DSM-Interrupt/FLP/FLP_PCB/FLP_PCB_terminal/mistance_PCB_terminal.kicad_sch

## KiCad design FLP_PCB/FLP_PCB_terminal/mistance_PCB_terminal.kicad_sch (2025-05-16)

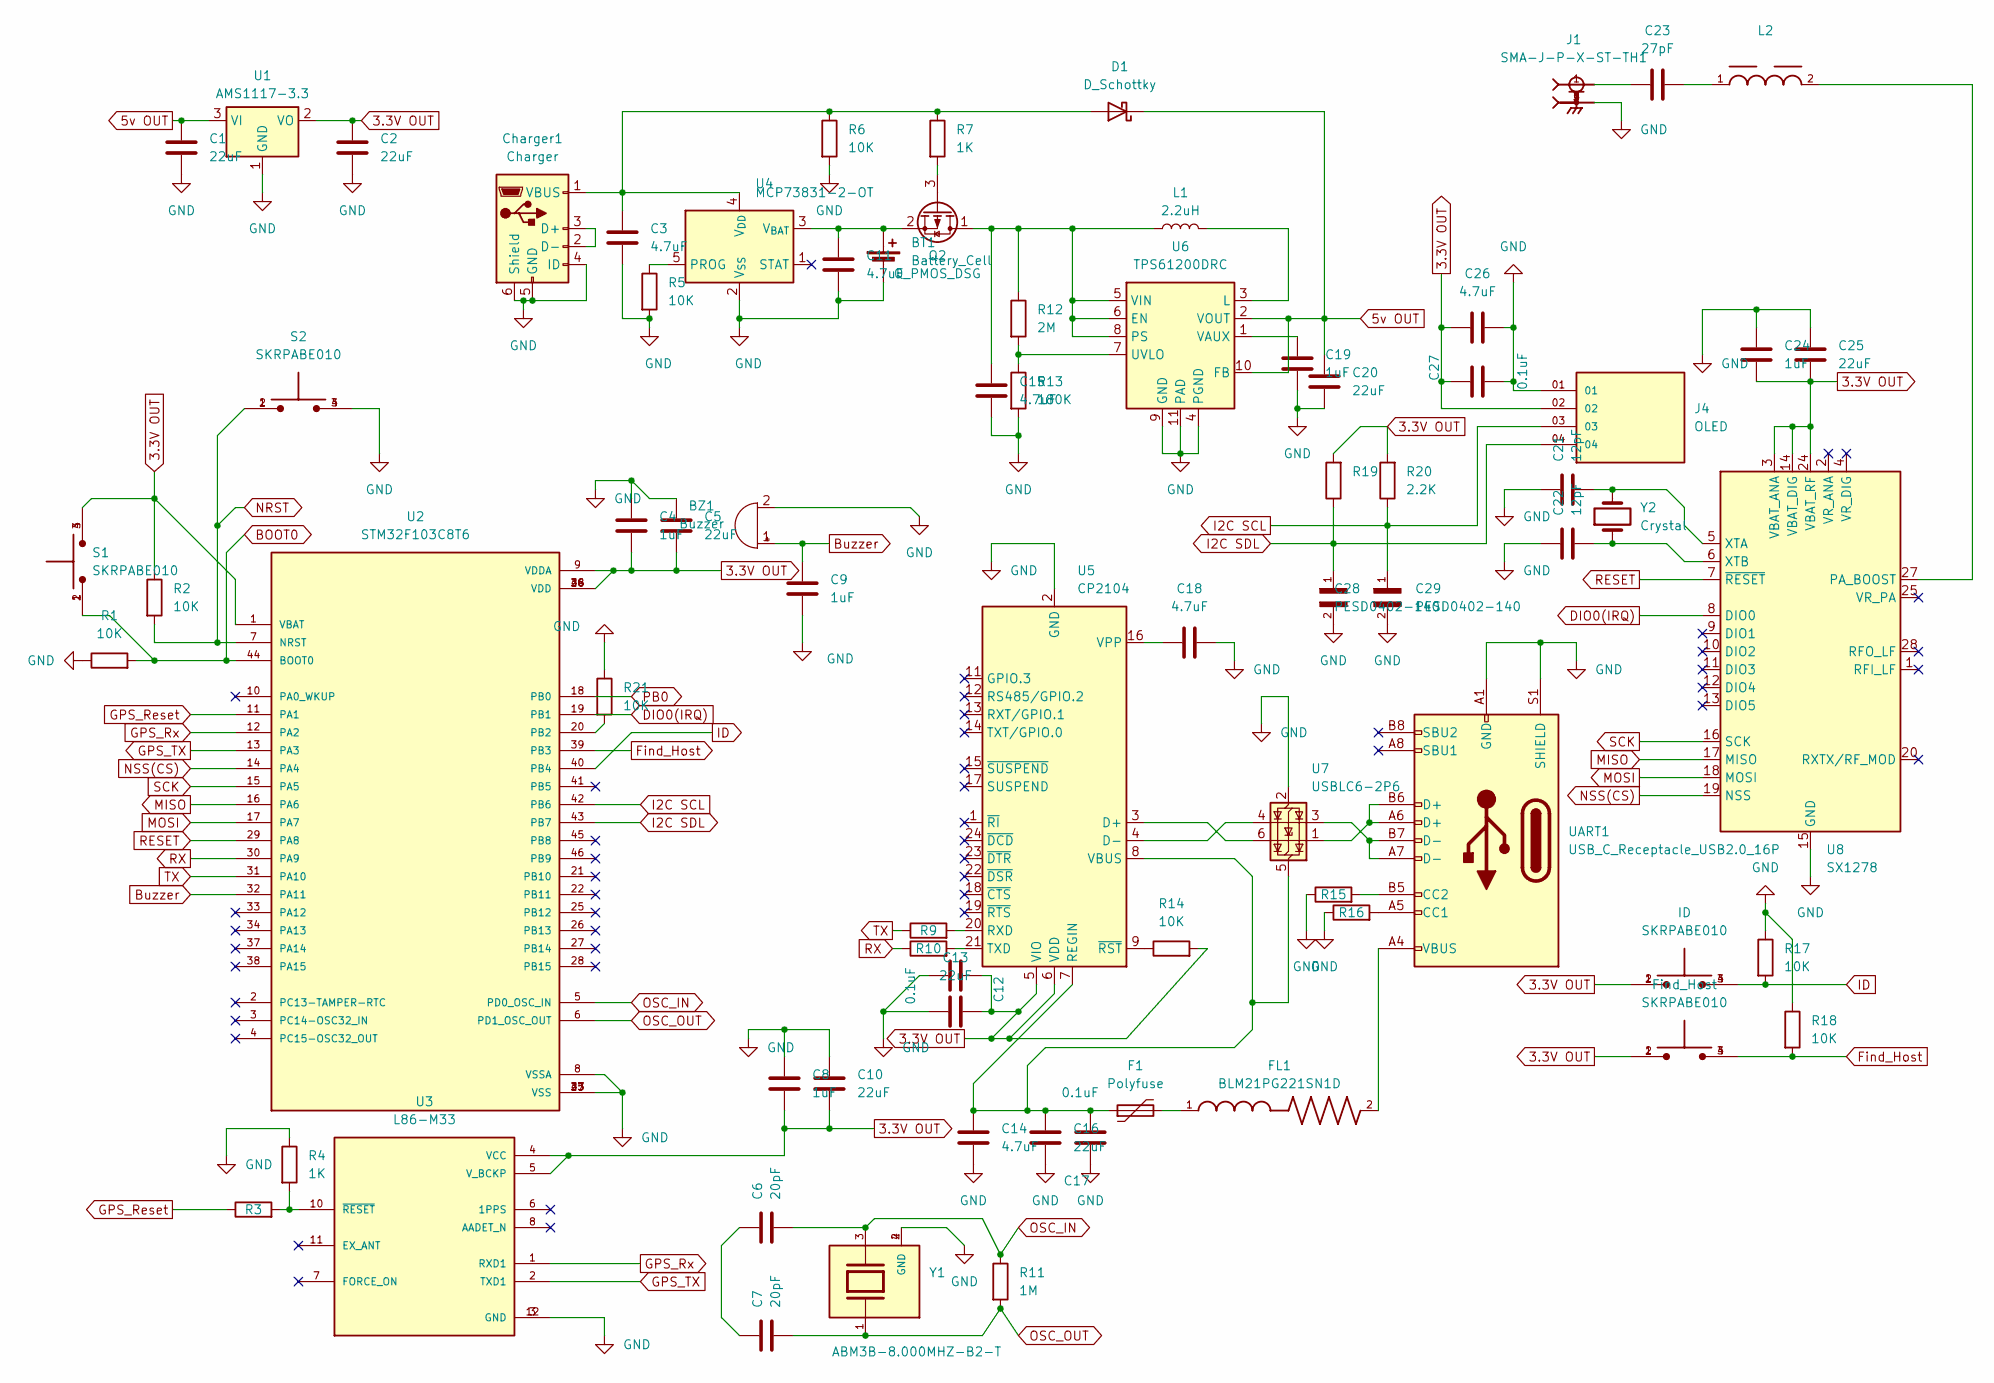
[picture p17: schematic mistance_PCB_terminal.kicad_sch]

Parts:
BT1: Battery_Cell; BatteryHolder_MPD_BH-18650-PC2
BZ1: Buzzer; Buzzer_15x7.5RM7.6
C1, C2, C5, C10, C13, C16, C20, C25: 22uF; C_0805_2012Metric
C3, C11, C14, C15, C18, C26: 4.7uF; C_0603_1608Metric
C4, C8, C9, C19, C24: 1uF; C_0603_1608Metric
C6, C7: 20pF; C_0402_1005Metric
C12, C17, C27: 0.1uF; C_0603_1608Metric
C21, C22: 12pF; C_0402_1005Metric
C23: 27pF; C_0603_1608Metric
C28, C29: PESD0402-140; RESC1005X35N
Charger1: Charger; USB_Micro-B_Amphenol_10103594-0001LF_Horizontal
D1: D_Schottky; DIOM5226X220N
F1: Polyfuse; R_0603_1608Metric
FL1: BLM21PG221SN1D; BEADC2012X105N
Find_Host: SKRPABE010; SW_SKRPABE010
ID: SKRPABE010; SW_SKRPABE010
J1: SMA-J-P-X-ST-TH1; SAMTEC_SMA-J-P-X-ST-TH1; PARTREV F
J4: OLED; SAMTEC_HTSW-104-20-TM-S; PARTREV R
L1: 2.2uH; L_1210_3225Metric
L2: WE-TPC_2811; DigiKey_Part_Number 732-3694-2-ND
Q2: Q_PMOS_DSG; SOT95P237X112-3N
R1, R2, R5, R6, R14, R17, R18, R21: 10K; R_0603_1608Metric
R3: 100R; R_0402_1005Metric
R4, R7: 1K; R_0603_1608Metric
R9, R10: 22R; R_0402_1005Metric
R11: 1M; R_0603_1608Metric
R12: 2M; R_1210_3225Metric
R13: 180K; R_1210_3225Metric
R15, R16: 5.1K; R_0402_1005Metric
R19, R20: 2.2K; R_0603_1608Metric
S1, S2: SKRPABE010; SW_SKRPABE010
U1: AMS1117-3.3; SOT-223-3_TabPin2
U2: STM32F103C8T6; QFP50P900X900X160-48N; PARTREV 10
U3: L86-M33; XCVR_L86-M33
U4: MCP73831-2-OT; SOT95P280X145-5N
U5: CP2104; QFN-24-1EP_4x4mm_P0.5mm_EP2.6x2.6mm
U6: TPS61200DRC; Texas_S-PVSON-N10_ThermalVias
U7: USBLC6-2P6; SOT-666
U8: SX1278; QFN-28-1EP_6x6mm_P0.65mm_EP4.8x4.8mm
UART1: USB_C_Receptacle_USB2.0_16P; AMPHENOL_12402012E212A
Y1: ABM3B-8.000MHZ-B2-T; XTAL_ABM3B-8.000MHZ-B2-T; PARTREV 08.25.15
Y2: Crystal; Crystal_SMD_2012-2Pin_2.0x1.2mm

Connections:
3.3V OUT: C2.1, C4.2, C5.2, C8.2, C10.2, C12.1, C13.2, C24.2, C25.2, C26.1, C27.1, Find_Host.1, Find_Host.2, ID.1, ID.2, J4.02, R2.1, R14.2, R19.2, R20.2, S1.3, S1.4, U1.2 (VO), U2.1 (VBAT), U2.9 (VDDA), U2.24 (VDD), U2.36 (VDD), U2.48 (VDD), U3.4 (VCC), U3.5 (V_BCKP), U5.5 (VIO), U5.6 (VDD), U8.3 (VBAT_ANA), U8.14 (VBAT_DIG), U8.24 (VBAT_RF)
5v OUT: C1.1, C20.1, D1.1 (K), U1.3 (VI), U6.2 (VOUT), U6.10 (FB)
BOOT0: R1.2, S1.1, S1.2, U2.44 (BOOT0)
Buzzer: BZ1.1 (+), C9.1, U2.32 (PA11)
DIO0(IRQ): U2.19 (PB1), U8.8 (DIO0)
Find_Host: Find_Host.3, Find_Host.4, R18.2, U2.39 (PB3)
GND: BT1.2 (-), BZ1.2 (-), C1.2, C2.2, C3.2, C4.1, C5.1, C8.1, C9.2, C10.1, C11.2, C12.2, C13.1, C14.2, C15.2, C16.2, C17.1, C18.2, C19.2, C20.2, C21.1, C22.1, C24.1, C25.1, C26.2, C27.2, C28.2, C29.2, Charger1.4 (ID), Charger1.5 (GND), Charger1.6 (Shield), J1.2, J1.3, J1.4, J1.5, J4.01, R1.1, R4.1, R5.2, R6.2, R13.2, R15.1, R16.1, R17.1, R18.1, R21.1, S2.3, S2.4, U1.1 (GND), U2.8 (VSSA), U2.23 (VSS), U2.35 (VSS), U2.47 (VSS), U3.3 (GND), U3.12 (GND), U4.2 (V_{SS}), U5.2 (GND), U5.25 (GND), U6.4 (PGND), U6.9 (GND), U6.11 (PAD), U7.2 (GND), U8.15 (GND), U8.21 (GND), U8.22 (GND), U8.23 (GND), U8.26 (GND), U8.29 (GND), UART1.A1 (GND), UART1.A12 (GND), UART1.B1 (GND), UART1.B12 (GND), UART1.S1 (SHIELD), Y1.2 (GND), Y1.4 (GND)
GPS_Reset: R3.1, U2.11 (PA1)
GPS_Rx: U2.12 (PA2), U3.1 (RXD1)
GPS_TX: U2.13 (PA3), U3.2 (TXD1)
I2C SCL: C29.1, J4.03, R20.1, U2.42 (PB6)
I2C SDL: C28.1, J4.04, R19.1, U2.43 (PB7)
ID: ID.3, ID.4, R17.2, U2.40 (PB4)
MISO: U2.16 (PA6), U8.17 (MISO)
MOSI: U2.17 (PA7), U8.18 (MOSI)
NRST: R2.2, S2.1, S2.2, U2.7 (NRST)
NSS(CS): U2.14 (PA4), U8.19 (NSS)
unnamed: BT1.1 (+), C11.1, Q2.2 (S), U4.3 (V_{BAT})
unnamed: C3.1, Charger1.1 (VBUS), D1.2 (A), R6.1, R7.1, U4.4 (V_{DD})
unnamed: C6.1, C7.1
unnamed: C14.1, C16.1, C17.2, F1.1, U5.7 (REGIN), U5.8 (VBUS), U7.5 (VBUS)
unnamed: C15.1, L1.1, Q2.1 (D), R12.1, U6.5 (VIN), U6.6 (EN), U6.8 (PS)
unnamed: C18.1, U5.16 (VPP)
unnamed: C19.1, U6.1 (VAUX)
unnamed: C21.2, U8.5 (XTA), Y2.2
unnamed: C22.2, U8.6 (XTB), Y2.1
unnamed: C23.1, J1.1
unnamed: C23.2, L2.1
unnamed: Charger1.2 (D-), Charger1.3 (D+)
unnamed: F1.2, FL1.1
unnamed: FL1.2, UART1.A4 (VBUS), UART1.A9 (VBUS), UART1.B4 (VBUS), UART1.B9 (VBUS)
unnamed: L1.2, U6.3 (L)
unnamed: L2.2, U8.27 (PA_BOOST)
unnamed: Q2.3 (G), R7.2
unnamed: R3.2, R4.2, U3.10 (~RESET)
unnamed: R5.1, U4.5 (PROG)
unnamed: R9.2, U5.20 (RXD)
unnamed: R10.2, U5.21 (TXD)
unnamed: R12.2, R13.1, U6.7 (UVLO)
unnamed: R14.1, U5.9 (~RST)
unnamed: R15.2, UART1.B5 (CC2)
unnamed: R16.2, UART1.A5 (CC1)
unnamed: R21.2, U2.20 (PB2)
unnamed: U5.3 (D+), U7.6 (I/O1)
unnamed: U5.4 (D-), U7.4 (I/O2)
unnamed: U7.1 (I/O1), UART1.A6 (D+), UART1.B6 (D+)
unnamed: U7.3 (I/O2), UART1.A7 (D-), UART1.B7 (D-)
OSC_IN: C6.2, R11.1, U2.5 (PD0_OSC_IN), Y1.3
OSC_OUT: C7.2, R11.2, U2.6 (PD1_OSC_OUT), Y1.1
PB0: U2.18 (PB0)
RESET: U2.29 (PA8), U8.7 (~RESET)
RX: R10.1, U2.30 (PA9)
SCK: U2.15 (PA5), U8.16 (SCK)
TX: R9.1, U2.31 (PA10)
